printfChins/Beyblade-RPM-Detector-Device/firmware/IR_Test/IR_Test.ino

#include <Arduino.h>
#include <Wire.h>
#include <stdio.h>
#include <string.h>

#define LED_GPIO                       8
#define IR1_GPIO                       3
#define IR2_GPIO                       1

/* [新增] ADC 測試腳位。 */
#define ADC_GPIO                       0

/*
 * [新增] 電池 ADC 分壓設定。
 *
 * BAT+ ---- 470k ----+---- GPIO4 / ADC
 *                    |
 *                   470k
 *                    |
 *                   GND
 *
 * VBAT = VADC * (R_TOP + R_BOTTOM) / R_BOTTOM
 *      = VADC * 2
 */
#define BAT_DIVIDER_R_TOP_OHM          470000UL
#define BAT_DIVIDER_R_BOTTOM_OHM       470000UL

/* [新增] IR 觸發電位。若實機黑白顯示相反，只需改成 LOW。 */
#define IR_TRIGGER_LEVEL               HIGH

/* [新增] OLED / I2C 設定。 */
#define OLED_SDA_GPIO                  20
#define OLED_SCL_GPIO                  21
#define OLED_I2C_ADDRESS               0x3C
#define OLED_I2C_FREQUENCY_HZ          400000UL
#define OLED_WIDTH                     128U
#define OLED_HEIGHT                    32U
#define OLED_PAGE_COUNT                (OLED_HEIGHT / 8U)
#define OLED_BUFFER_SIZE               ((OLED_WIDTH * OLED_HEIGHT) / 8U)
#define OLED_UPDATE_INTERVAL_MS        50UL
#define OLED_I2C_DATA_CHUNK_SIZE       16U

/*
 * [新增] ADC 穩定取樣參數。
 * 470k / 470k 分壓的等效源阻抗很高，先丟棄數次轉換，
 * 再以較慢節奏做多次平均，避免第一次取樣偏低。
 */
#define ADC_DISCARD_SAMPLES             8U
#define ADC_AVERAGE_SAMPLES             64U
#define ADC_SAMPLE_DELAY_US             100U

#define digitalToggle(x) digitalWrite(x, !digitalRead(x))

/* [新增] OLED framebuffer。 */
static uint8_t g_oled_buffer[OLED_BUFFER_SIZE];
static bool g_oled_ready = false;
static uint32_t g_oled_last_update_ms = 0UL;

int ls_IR1 = -1;
int ls_IR2 = -1;

/* =========================================================
 * [新增] SSD1306 OLED 基礎驅動
 * ========================================================= */
static bool oledWriteCommands(const uint8_t *commands, size_t length) {
  if ((commands == nullptr) || (length == 0U)) {
    return false;
  }

  Wire.beginTransmission(OLED_I2C_ADDRESS);
  Wire.write(0x00U);
  Wire.write(commands, length);

  return (Wire.endTransmission() == 0U);
}

static bool oledWriteData(const uint8_t *data, size_t length) {
  size_t offset = 0U;

  if ((data == nullptr) || (length == 0U)) {
    return false;
  }

  while (offset < length) {
    size_t chunkLength = length - offset;

    if (chunkLength > OLED_I2C_DATA_CHUNK_SIZE) {
      chunkLength = OLED_I2C_DATA_CHUNK_SIZE;
    }

    Wire.beginTransmission(OLED_I2C_ADDRESS);
    Wire.write(0x40U);
    Wire.write(&data[offset], chunkLength);

    if (Wire.endTransmission() != 0U) {
      return false;
    }

    offset += chunkLength;
  }

  return true;
}

static bool oledProbe(void) {
  Wire.beginTransmission(OLED_I2C_ADDRESS);
  return (Wire.endTransmission() == 0U);
}

static void oledClearBuffer(void) {
  memset(g_oled_buffer, 0, sizeof(g_oled_buffer));
}

static void oledSetPixel(uint8_t x, uint8_t y, bool on) {
  uint16_t index;
  uint8_t mask;

  if ((x >= OLED_WIDTH) || (y >= OLED_HEIGHT)) {
    return;
  }

  index = (uint16_t)x + ((uint16_t)(y / 8U) * OLED_WIDTH);
  mask = (uint8_t)(1U << (y & 0x07U));

  if (on == true) {
    g_oled_buffer[index] |= mask;
  } else {
    g_oled_buffer[index] &= (uint8_t)(~mask);
  }
}

static void oledDrawHorizontalLine(uint8_t x, uint8_t y, uint8_t width) {
  uint16_t i;

  for (i = 0U; i < width; i++) {
    oledSetPixel((uint8_t)(x + i), y, true);
  }
}

static void oledDrawVerticalLine(uint8_t x, uint8_t y, uint8_t height) {
  uint16_t i;

  for (i = 0U; i < height; i++) {
    oledSetPixel(x, (uint8_t)(y + i), true);
  }
}

static void oledDrawRect(uint8_t x, uint8_t y, uint8_t width, uint8_t height) {
  if ((width < 2U) || (height < 2U)) {
    return;
  }

  oledDrawHorizontalLine(x, y, width);
  oledDrawHorizontalLine(x, (uint8_t)(y + height - 1U), width);
  oledDrawVerticalLine(x, y, height);
  oledDrawVerticalLine((uint8_t)(x + width - 1U), y, height);
}

static void oledFillRect(uint8_t x, uint8_t y, uint8_t width, uint8_t height) {
  uint16_t px;
  uint16_t py;

  for (py = 0U; py < height; py++) {
    for (px = 0U; px < width; px++) {
      oledSetPixel((uint8_t)(x + px), (uint8_t)(y + py), true);
    }
  }
}

/*
 * [新增] 5x7 字型。
 * 測試畫面只保留需要的字元：0~9、A/C/D/I/R/V、空白、小數點。
 */
static const uint8_t *oledGetGlyph(char c) {
  static const uint8_t glyphSpace[5] = {0x00, 0x00, 0x00, 0x00, 0x00};
  static const uint8_t glyphDot[5]   = {0x00, 0x60, 0x60, 0x00, 0x00};
  static const uint8_t glyph0[5]     = {0x3E, 0x51, 0x49, 0x45, 0x3E};
  static const uint8_t glyph1[5]     = {0x00, 0x42, 0x7F, 0x40, 0x00};
  static const uint8_t glyph2[5]     = {0x42, 0x61, 0x51, 0x49, 0x46};
  static const uint8_t glyph3[5]     = {0x21, 0x41, 0x45, 0x4B, 0x31};
  static const uint8_t glyph4[5]     = {0x18, 0x14, 0x12, 0x7F, 0x10};
  static const uint8_t glyph5[5]     = {0x27, 0x45, 0x45, 0x45, 0x39};
  static const uint8_t glyph6[5]     = {0x3C, 0x4A, 0x49, 0x49, 0x30};
  static const uint8_t glyph7[5]     = {0x01, 0x71, 0x09, 0x05, 0x03};
  static const uint8_t glyph8[5]     = {0x36, 0x49, 0x49, 0x49, 0x36};
  static const uint8_t glyph9[5]     = {0x06, 0x49, 0x49, 0x29, 0x1E};
  static const uint8_t glyphA[5]     = {0x7E, 0x11, 0x11, 0x11, 0x7E};
  /* [新增] BAT 顯示需要 B / T。 */
  static const uint8_t glyphB[5]     = {0x7F, 0x49, 0x49, 0x49, 0x36};
  static const uint8_t glyphC[5]     = {0x3E, 0x41, 0x41, 0x41, 0x22};
  static const uint8_t glyphD[5]     = {0x7F, 0x41, 0x41, 0x22, 0x1C};
  static const uint8_t glyphI[5]     = {0x00, 0x41, 0x7F, 0x41, 0x00};
  static const uint8_t glyphR[5]     = {0x7F, 0x09, 0x19, 0x29, 0x46};
  /* [新增] BAT 顯示需要 T。 */
  static const uint8_t glyphT[5]     = {0x01, 0x01, 0x7F, 0x01, 0x01};
  static const uint8_t glyphV[5]     = {0x1F, 0x20, 0x40, 0x20, 0x1F};

  switch (c) {
    case '0': return glyph0;
    case '1': return glyph1;
    case '2': return glyph2;
    case '3': return glyph3;
    case '4': return glyph4;
    case '5': return glyph5;
    case '6': return glyph6;
    case '7': return glyph7;
    case '8': return glyph8;
    case '9': return glyph9;
    case 'A': return glyphA;
    case 'B': return glyphB;
    case 'C': return glyphC;
    case 'D': return glyphD;
    case 'I': return glyphI;
    case 'R': return glyphR;
    case 'T': return glyphT;
    case 'V': return glyphV;
    case '.': return glyphDot;
    case ' ':
    default:
      return glyphSpace;
  }
}

static void oledDrawChar(uint8_t x, uint8_t y, char c) {
  const uint8_t *glyph = oledGetGlyph(c);
  uint8_t column;
  uint8_t row;

  for (column = 0U; column < 5U; column++) {
    for (row = 0U; row < 7U; row++) {
      if ((glyph[column] & (1U << row)) != 0U) {
        oledSetPixel((uint8_t)(x + column), (uint8_t)(y + row), true);
      }
    }
  }
}

static void oledDrawText(uint8_t x, uint8_t y, const char *text) {
  uint8_t cursorX = x;

  if (text == nullptr) {
    return;
  }

  while (*text != '\0') {
    oledDrawChar(cursorX, y, *text);
    cursorX = (uint8_t)(cursorX + 6U);
    text++;
  }
}

static bool oledFlush(void) {
  const uint8_t setAddressCommands[] = {
    0x21U, 0x00U, (uint8_t)(OLED_WIDTH - 1U),
    0x22U, 0x00U, (uint8_t)(OLED_PAGE_COUNT - 1U)
  };

  if (oledWriteCommands(setAddressCommands, sizeof(setAddressCommands)) == false) {
    return false;
  }

  return oledWriteData(g_oled_buffer, sizeof(g_oled_buffer));
}

static bool oledBegin(void) {
  const uint8_t initCommands[] = {
    0xAEU,
    0xD5U, 0x80U,
    0xA8U, 0x1FU,
    0xD3U, 0x00U,
    0x40U,
    0x8DU, 0x14U,
    0x20U, 0x00U,
    /* [修改] OLED 旋轉 180 度：SEG remap normal + COM scan normal。 */
    0xA0U,
    0xC0U,
    0xDAU, 0x02U,
    0x81U, 0x8FU,
    0xD9U, 0xF1U,
    0xDBU, 0x40U,
    0xA4U,
    0xA6U,
    0xAFU
  };

  Wire.begin(OLED_SDA_GPIO, OLED_SCL_GPIO);
  Wire.setClock(OLED_I2C_FREQUENCY_HZ);

  if (oledProbe() == false) {
    return false;
  }

  if (oledWriteCommands(initCommands, sizeof(initCommands)) == false) {
    return false;
  }

  oledClearBuffer();

  if (oledFlush() == false) {
    return false;
  }

  return true;
}

/* =========================================================
 * [新增] ADC 與測試畫面
 * ========================================================= */
static uint32_t readAdcMilliVolts(void) {
  uint64_t totalMilliVolts = 0ULL;
  uint8_t i;

  /*
   * [修改]
   * 先做數次 dummy read，讓 ADC 前端與外部分壓節點穩定。
   */
  for (i = 0U; i < ADC_DISCARD_SAMPLES; i++) {
    (void)analogReadMilliVolts(ADC_GPIO);
    delayMicroseconds(ADC_SAMPLE_DELAY_US);
  }

  /*
   * [修改]
   * 使用 64 次 calibrated mV 取樣平均。
   */
  for (i = 0U; i < ADC_AVERAGE_SAMPLES; i++) {
    totalMilliVolts += (uint32_t)analogReadMilliVolts(ADC_GPIO);
    delayMicroseconds(ADC_SAMPLE_DELAY_US);
  }

  return (uint32_t)(totalMilliVolts / ADC_AVERAGE_SAMPLES);
}

/*
 * [新增] 將 GPIO4 ADC 電壓換算回電池端電壓。
 *
 * 470k / 470k：
 * VBAT = VADC * 2
 *
 * 使用 uint64_t 避免乘法中間值溢位。
 */
static uint32_t readBatteryMilliVolts(void) {
  uint32_t adcMilliVolts;
  uint64_t batteryMilliVolts;

  adcMilliVolts = readAdcMilliVolts();

  batteryMilliVolts =
      ((uint64_t)adcMilliVolts *
       (BAT_DIVIDER_R_TOP_OHM + BAT_DIVIDER_R_BOTTOM_OHM)) /
      BAT_DIVIDER_R_BOTTOM_OHM;

  return (uint32_t)batteryMilliVolts;
}

static void oledDrawIrState(uint8_t x, uint8_t y, bool triggered) {
  const uint8_t boxSize = 12U;

  if (triggered == true) {
    /* [需求] 全黑方塊 = IR 觸發。 */
    oledFillRect(x, y, boxSize, boxSize);
  } else {
    /* [需求] 空心方塊 = IR 未觸發。 */
    oledDrawRect(x, y, boxSize, boxSize);
  }
}

static void oledUpdate(int ir1, int ir2) {
  uint32_t nowMs = millis();
  uint32_t batteryMilliVolts;
  bool ir1Triggered;
  bool ir2Triggered;
  char batteryText[16];

  if (g_oled_ready == false) {
    return;
  }

  if ((uint32_t)(nowMs - g_oled_last_update_ms) < OLED_UPDATE_INTERVAL_MS) {
    return;
  }

  g_oled_last_update_ms = nowMs;

  ir1Triggered = (ir1 == IR_TRIGGER_LEVEL);
  ir2Triggered = (ir2 == IR_TRIGGER_LEVEL);
  batteryMilliVolts = readBatteryMilliVolts();

  snprintf(batteryText,
           sizeof(batteryText),
           "BAT %lu.%03luV",
           (unsigned long)(batteryMilliVolts / 1000UL),
           (unsigned long)(batteryMilliVolts % 1000UL));

  oledClearBuffer();

  /* 第一列：IR1 / IR2 狀態。 */
  oledDrawText(0U, 3U, "IR1");
  oledDrawIrState(20U, 1U, ir1Triggered);

  oledDrawText(48U, 3U, "IR2");
  oledDrawIrState(68U, 1U, ir2Triggered);

  /* [修改] 第二列：顯示 470k / 470k 分壓換算後的電池端電壓。 */
  oledDrawText(0U, 21U, batteryText);

  oledFlush();
}

void setup() {
  pinMode(LED_GPIO, OUTPUT);
  pinMode(IR1_GPIO, INPUT);
  pinMode(IR2_GPIO, INPUT);
  /* [新增] 明確設定 ADC GPIO 為輸入。 */
  pinMode(ADC_GPIO, INPUT);

  digitalWrite(LED_GPIO, LOW);

  /* [新增] ADC 設定：12-bit、11 dB attenuation。 */
  analogReadResolution(12);
  analogSetPinAttenuation(ADC_GPIO, ADC_11db);

  /* [新增] 初始化 OLED。 */
  g_oled_ready = oledBegin();
  g_oled_last_update_ms = 0UL;
}

void loop() {
  int IR1 = digitalRead(IR1_GPIO);
  int IR2 = digitalRead(IR2_GPIO);

  if (IR1 != ls_IR1 || IR2 != ls_IR2) {
    digitalToggle(LED_GPIO);
    ls_IR1 = IR1;
    ls_IR2 = IR2;
  }

  /* [修改] 更新 OLED：IR 方塊 + 電池端電壓。 */
  oledUpdate(IR1, IR2);

  delay(10);
}
